liamhays/sharpie/sharpie-formatter/the_gang/original_frame.png

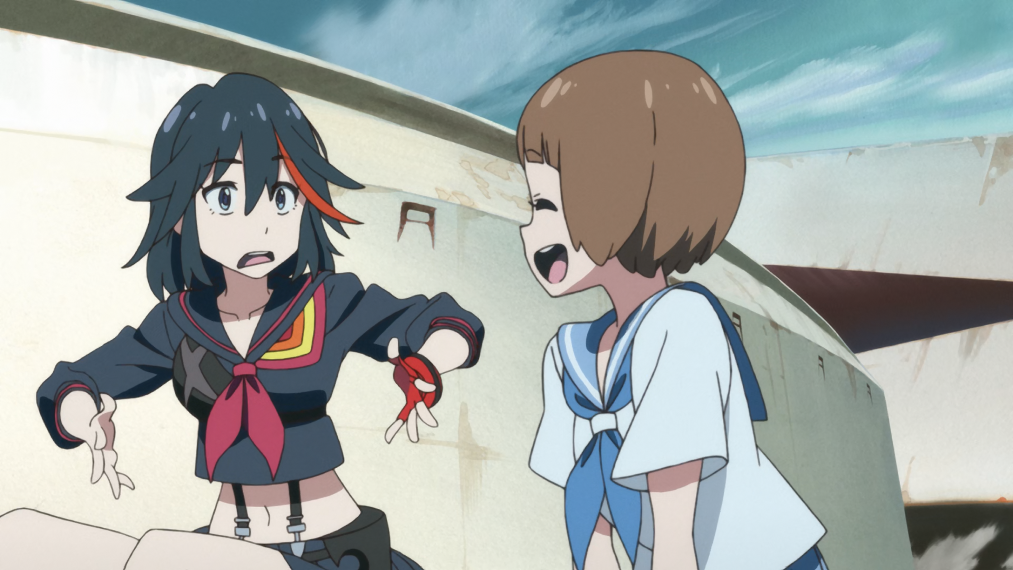
sharpie-formatter/the_gang/original_frame.png
