liamhays/sharpie/sharpie-formatter/the_gang/original_frame_4_3.png

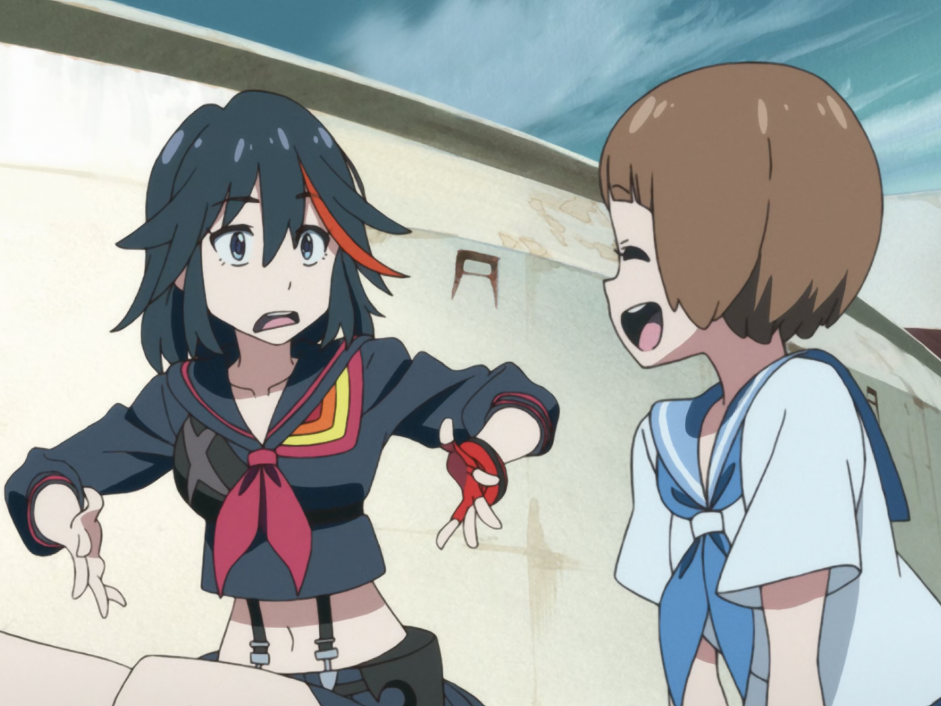
sharpie-formatter/the_gang/original_frame_4_3.png
