liamhays/sharpie/sharpie-sw/pencils.h

// This is xxd-generated data of a image of colored pencils, correctly
// cropped and rotated, then dithered. It's a great static test image
// because it shows off the color potential of the Sharpie display.

unsigned char pencils[] = {
  0x3f, 0x3f, 0x3f, 0x3f, 0x3f, 0x3f, 0x3f, 0x3f, 0x3f, 0x3f, 0x1f, 0x07,
  0x0f, 0x1f, 0x1f, 0x2b, 0x2f, 0x3f, 0x3f, 0x3f, 0x3f, 0x3f, 0x3f, 0x3f,
  0x3f, 0x3f, 0x3f, 0x3f, 0x3f, 0x3f, 0x3f, 0x3f, 0x3f, 0x3f, 0x3f, 0x3f,
  0x3f, 0x3f, 0x3f, 0x3f, 0x3f, 0x3f, 0x3f, 0x3f, 0x3f, 0x3f, 0x3f, 0x1f,
  0x3f, 0x3f, 0x1f, 0x1f, 0x3f, 0x2f, 0x2f, 0x0f, 0x1f, 0x0f, 0x0b, 0x0b,
  0x0b, 0x0b, 0x03, 0x03, 0x03, 0x03, 0x03, 0x02, 0x02, 0x03, 0x0b, 0x1b,
  0x3f, 0x3f, 0x3f, 0x3f, 0x3f, 0x3f, 0x3f, 0x3f, 0x3f, 0x3f, 0x1f, 0x1b,
  0x1f, 0x1f, 0x1f, 0x3f, 0x2f, 0x1f, 0x1b, 0x1b, 0x1b, 0x3b, 0x27, 0x27,
  0x2f, 0x2b, 0x2b, 0x23, 0x27, 0x07, 0x17, 0x17, 0x17, 0x03, 0x23, 0x27,
  0x03, 0x03, 0x03, 0x07, 0x07, 0x03, 0x03, 0x03, 0x03, 0x03, 0x03, 0x03,
  0x07, 0x17, 0x27, 0x07, 0x07, 0x07, 0x01, 0x03, 0x02, 0x03, 0x21, 0x38,
  0x32, 0x22, 0x22, 0x17, 0x13, 0x03, 0x0b, 0x03, 0x07, 0x0b, 0x03, 0x07,
  0x07, 0x07, 0x07, 0x07, 0x27, 0x2f, 0x0b, 0x1b, 0x0b, 0x0b, 0x03, 0x03,
  0x0b, 0x03, 0x07, 0x07, 0x07, 0x07, 0x03, 0x03, 0x07, 0x0b, 0x03, 0x27,
  0x0b, 0x03, 0x27, 0x22, 0x03, 0x13, 0x11, 0x33, 0x22, 0x32, 0x36, 0x34,
  0x35, 0x35, 0x2e, 0x2e, 0x0c, 0x08, 0x08, 0x11, 0x25, 0x2e, 0x37, 0x27,
  0x03, 0x03, 0x0b, 0x03, 0x07, 0x0b, 0x03, 0x07, 0x0b, 0x03, 0x23, 0x27,
  0x23, 0x23, 0x23, 0x03, 0x13, 0x23, 0x27, 0x27, 0x27, 0x07, 0x1b, 0x1b,
  0x13, 0x17, 0x17, 0x1f, 0x1b, 0x3b, 0x2b, 0x2b, 0x2b, 0x3f, 0x1f, 0x1b,
  0x3f, 0x3e, 0x3f, 0x3b, 0x3b, 0x3d, 0x3f, 0x3e, 0x32, 0x00, 0x00, 0x00,
  0x3f, 0x3f, 0x3f, 0x3f, 0x3f, 0x3f, 0x3f, 0x3f, 0x3f, 0x3f, 0x3f, 0x27,
  0x27, 0x07, 0x17, 0x1f, 0x1f, 0x2f, 0x3f, 0x3f, 0x3f, 0x3f, 0x3f, 0x3f,
  0x3f, 0x3f, 0x3f, 0x3f, 0x3f, 0x3f, 0x3f, 0x3f, 0x3f, 0x3f, 0x3f, 0x3f,
  0x3f, 0x3f, 0x3f, 0x3f, 0x3f, 0x2f, 0x1f, 0x1f, 0x1f, 0x3f, 0x2f, 0x2f,
  0x1f, 0x1f, 0x1f, 0x1f, 0x3f, 0x1f, 0x1f, 0x1f, 0x2f, 0x0f, 0x07, 0x07,
  0x07, 0x07, 0x0b, 0x03, 0x03, 0x03, 0x02, 0x02, 0x02, 0x03, 0x27, 0x2f,
  0x1f, 0x3f, 0x3f, 0x3f, 0x3f, 0x3f, 0x3f, 0x3f, 0x3f, 0x1f, 0x17, 0x17,
  0x3f, 0x2f, 0x2f, 0x2f, 0x1f, 0x1f, 0x17, 0x17, 0x17, 0x1f, 0x1b, 0x1f,
  0x1b, 0x17, 0x17, 0x17, 0x17, 0x17, 0x17, 0x17, 0x1b, 0x13, 0x17, 0x1b,
  0x03, 0x03, 0x03, 0x17, 0x03, 0x03, 0x03, 0x03, 0x03, 0x03, 0x03, 0x03,
  0x09, 0x0b, 0x09, 0x0b, 0x12, 0x09, 0x03, 0x02, 0x06, 0x08, 0x01, 0x19,
  0x18, 0x3a, 0x2a, 0x20, 0x22, 0x12, 0x01, 0x03, 0x03, 0x03, 0x0b, 0x03,
  0x0b, 0x03, 0x03, 0x0b, 0x0b, 0x03, 0x17, 0x07, 0x03, 0x03, 0x07, 0x0a,
  0x03, 0x03, 0x03, 0x07, 0x03, 0x13, 0x25, 0x23, 0x23, 0x07, 0x13, 0x11,
  0x21, 0x23, 0x22, 0x22, 0x0a, 0x22, 0x22, 0x22, 0x12, 0x32, 0x38, 0x39,
  0x3a, 0x38, 0x34, 0x1c, 0x1c, 0x1c, 0x19, 0x25, 0x25, 0x3c, 0x19, 0x13,
  0x22, 0x03, 0x03, 0x03, 0x03, 0x03, 0x03, 0x03, 0x03, 0x23, 0x2b, 0x2b,
  0x03, 0x13, 0x13, 0x13, 0x23, 0x23, 0x2b, 0x2b, 0x2b, 0x23, 0x27, 0x23,
  0x27, 0x2b, 0x2b, 0x2a, 0x2b, 0x2b, 0x2b, 0x29, 0x25, 0x2d, 0x29, 0x27,
  0x3e, 0x3e, 0x3e, 0x2a, 0x3e, 0x3e, 0x3c, 0x3d, 0x3d, 0x10, 0x10, 0x10,
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
};
unsigned int pencils_raw_len = 76800;
