liamhays/sharpie/sharpie-usb-display/usb-display-client/tusb_config.h

/*
 * The MIT License (MIT)
 *
 * Copyright (c) 2019 Ha Thach (tinyusb.org)
 *
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
 */

#ifndef _TUSB_CONFIG_H_
#define _TUSB_CONFIG_H_

//--------------------------------------------------------------------
// COMMON CONFIGURATION
//--------------------------------------------------------------------

// RHPort number used for device can be defined by board.mk, default to port 0
#ifndef BOARD_DEVICE_RHPORT_NUM
  #define BOARD_DEVICE_RHPORT_NUM     0
#endif

// RHPort max operational speed can defined by board.mk
#define BOARD_DEVICE_RHPORT_SPEED   OPT_MODE_FULL_SPEED

// Device mode with rhport and speed defined by board.mk
#define CFG_TUSB_RHPORT0_MODE   (OPT_MODE_DEVICE)

// CFG_TUSB_DEBUG is defined by compiler in DEBUG build
// #define CFG_TUSB_DEBUG           0

/* USB DMA on some MCUs can only access a specific SRAM region with restriction on alignment.
 * Tinyusb use follows macros to declare transferring memory so that they can be put
 * into those specific section.
 * e.g
 * - CFG_TUSB_MEM SECTION : __attribute__ (( section(".usb_ram") ))
 * - CFG_TUSB_MEM_ALIGN   : __attribute__ ((aligned(4)))
 */
#ifndef CFG_TUSB_MEM_SECTION
#define CFG_TUSB_MEM_SECTION
#endif

#ifndef CFG_TUSB_MEM_ALIGN
#define CFG_TUSB_MEM_ALIGN          __attribute__ ((aligned(4)))
#endif

//--------------------------------------------------------------------
// DEVICE CONFIGURATION
//--------------------------------------------------------------------

#ifndef CFG_TUD_ENDPOINT0_SIZE
#define CFG_TUD_ENDPOINT0_SIZE    64
#endif

//------------- CLASS -------------//
#define CFG_TUD_CDC               0
#define CFG_TUD_MSC               0
#define CFG_TUD_HID               0
#define CFG_TUD_MIDI              0
#define CFG_TUD_VENDOR            1

#define CFG_TUD_VENDOR_TX_BUFSIZE   (64)
#define CFG_TUD_VENDOR_RX_BUFSIZE   (32768)

#ifdef __cplusplus
 }
#endif

#endif /* _TUSB_CONFIG_H_ */
